Cybdo/cybdokey/assets/renders/front_and_back_1440p.png

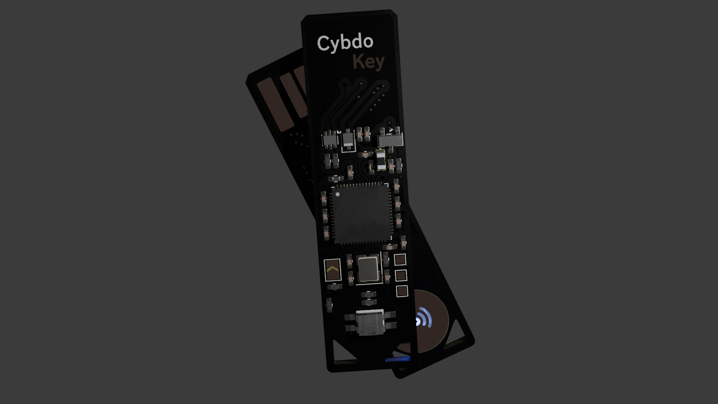
assets/renders/front_and_back_1440p.png
